Flowm/move-on-helium-sensors/doc/img/Gas.png

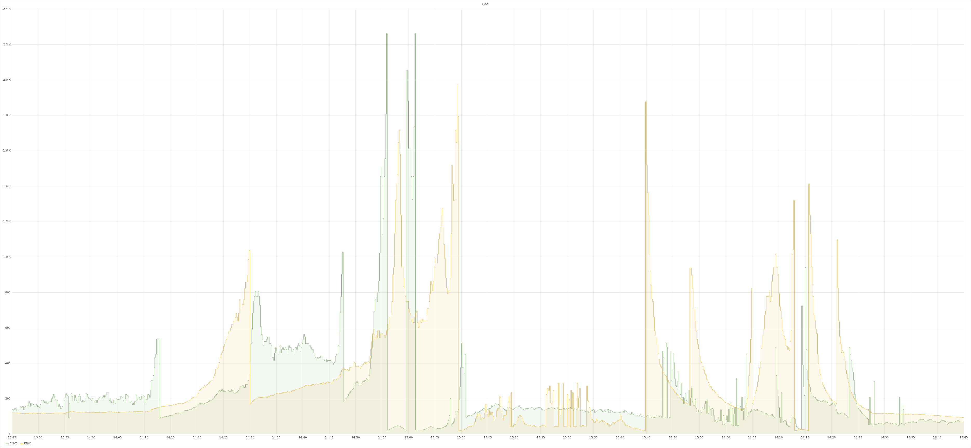
doc/img/Gas.png
