Flowm/move-on-helium-sensors/doc/img/TOSS_Photo.png

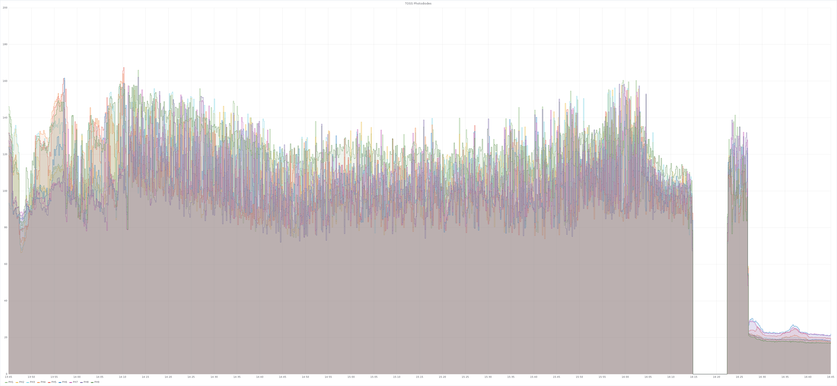
doc/img/TOSS_Photo.png
