Flowm/move-on-helium-sensors/src/modules/ADC/MPC320X.hpp

/*
 * MPC320X.h
 *
 *  Created on: Dec 16, 2017
 *      Author: tkale
 */
#pragma once

#include <mbed.h>

#define MPC_CHANNELS 8 // 0-7 : 8 channels on the MPC3208


/**
 * Driver for the MPC230X ADC's.
 * Configure the last digit of the device as the number of channels above.
 * WARNING: Only tested on the MPC2308!
 */
class MPC320X {
public:
    MPC320X(SPI &spi, DigitalOut &chipSelect) :
        spi(spi),
        chipSelect(chipSelect)
        {};
    /**
     * Read a adcs value from a single channel.
     * @param channel [0-7] : What channel to read.
     * @return
     */
    uint16_t getValueSingle(uint8_t channel);
    /**
     * Read a difference between 2 consecutive channels
     * TODO
     * @param channel
     * @return
     */
    uint16_t getValueDifferential(uint8_t channel);
    /**
     * Tests all channels in single ended mode and prints the result on stdout.
     */
    void testAllChannels();
private:
    //Interfaces
    SPI& spi;
    DigitalOut& chipSelect;
};
