Flowm/move-on-helium-sensors/tools/grafana/bin/sensor-parser/moveon-sen-parser.cpp

#include <cstdio>
#include <cstdint>
#include <cstddef>
#include <string>
#include "../../../../src/include/protocol_sensors.h"
#include <math.h>


float calculateDensity(float pressure, float temperature){

  //pressure [Pa], temperature [°C]
  //calculate current density [kg/m^3]

  int selector = 0;
  const float Rs = 287.1; //gas constant of air J/(kg*K);

  int N = 10;
  float nominaldensity[N] = {1.225, 3.899e-2, 1.774e-2, 3.972e-3, 1.057e-3, 3.206e-4, 8.77e-5, 1.905e-5, 3.396e-6, 5.297e-7};
  float basealtitude[N] = {0, 25, 30, 40, 50, 60, 70, 80, 90, 100};
  float scaleheight[N] = {7.249, 6.349, 6.682, 7.554, 8.382, 7.714, 6.549, 5.799, 5.382, 5.877};

  float density = pressure / (Rs * (temperature+273.15));
  for(int i = 0; i < N && density < nominaldensity[i]; i++) {
    selector = i;
  }

  float currentaltitudedensity = (basealtitude[selector] - log(density/nominaldensity[selector])*scaleheight[selector])*1000;
  return currentaltitudedensity;
}

float calculatePressure(float pressure){
  float currentaltitudepressure = - 8435 * log(pressure / 101325);
  return currentaltitudepressure;
}

int main(int argc, char **argv) {
    int c;
    int s = 0;
    int invalid = 0;
    char buf[1000];

    // Read binary data from stdin
    while((c = getchar()) != EOF) {
        buf[s++] = c;
    }

    printf("DBG SIZE=%d EXP=%d", s, sizeof(SensorDataNoGps));
    if (argc == 2) {
        invalid = std::stoi(argv[1]);
        printf(",CHK=%d", invalid);
    }
    printf("\r\n");

    // Invalid byte to packet size
    int invalid_range_start[8] = {};
    int invalid_count = 0;
    for (int i=0; i<8; i++) {
        if (invalid & (1 << i)) {
            invalid_count++;
            invalid_range_start[i] = 30 + 32 * i;
            printf("DBG Invalid Chunk %d from byte %d\n", i, invalid_range_start[i]);
        }
    }

    //if (invalid_count > 3) {
    //    printf("DBG Too many invalid chunks %d\n", invalid_count);
    //    return 1;
    //}

    // Cast to datastructure and print
    SensorDataNoGps* data = (SensorDataNoGps*) buf;

    //if (!(invalid & 0x01)) {
    for (int i = 0; i < MAX_ENV_SENSORS; i++) {
        printf("ENV%d "
               "TEMP=%.2f,HUM=%.2f,PRES=%.2f,GAS=%.4f,"
               "PALT=%.2f,DALT=%.2f"
               "\r\n",
               i,
               data->env[i].temperature,
               data->env[i].humidity,
               data->env[i].pressure,
               data->env[i].gasresistance,
               calculatePressure(data->env[i].pressure * 100),
               calculateDensity(data->env[i].pressure * 100, data->env[i].temperature));
    }
    //}

    //if (!(invalid & 0x03)) {
    printf("IMU "
           "ACC_X=%.4f,ACC_Y=%.4f,ACC_Z=%.4f,"
           "GYRO_X=%.4f,GYRO_Y=%.4f,GYRO_Z=%.4f,"
           "MAG_X=%.2f,MAG_Y=%.2f,MAG_Z=%.2f,"
           "ANG_X=%.4f,ANG_Y=%.4f,ANG_Z=%.4f,"
           //"QUAT_W=%.4f,QUAT_X=%.4f,QUAT_Y=%.4f,QUAT_Z=%.4f,"
           "TEMP_ACC=%d,"
           "RSTS=%u"
           "\r\n",
           data->imu.accel.x, data->imu.accel.y, data->imu.accel.z,
           data->imu.gyro.x, data->imu.gyro.y, data->imu.gyro.z,
           data->imu.mag.x, data->imu.mag.y, data->imu.mag.z,
           data->imu.orientation.x, data->imu.orientation.y, data->imu.orientation.z,
           //data->imu.quaternion.w, data->imu.quaternion.x, data->imu.quaternion.y, data->imu.quaternion.z,
           data->imu.temp_accel, //data->imu.temp_gyro,
           data->imu.resets);
    //}

    //if (!(invalid & 0x0C)) {
    printf("ADCS "
           //"ACC_X=%.4f,ACC_Y=%.4f,ACC_Z=%.4f,"
           "GYRO_X=%.4f,GYRO_Y=%.4f,GYRO_Z=%.4f,"
           "MAG_X=%.4f,MAG_Y=%.4f,MAG_Z=%.4f,"
           "SUN_X=%.4f,SUN_Y=%.4f,SUN_Z=%.4f,"
           "TEMP_OW1=%.4f,TEMP_OW2=%.4f,TEMP_OW3=%.4f,"
           "SUN_RAW1=%hu,SUN_RAW2=%hu,SUN_RAW3=%hu,SUN_RAW4=%hu"
           "\r\n",
           //data->adcs.accel.x, data->adcs.accel.y, data->adcs.accel.z,
           data->adcs.gyro.x, data->adcs.gyro.y, data->adcs.gyro.z,
           data->adcs.mag.x, data->adcs.mag.y, data->adcs.mag.z,
           data->adcs.sun.x, data->adcs.sun.y, data->adcs.sun.z,
           data->adcs.temp[0], data->adcs.temp[1], data->adcs.temp[2],
           data->adcs.raw_sun[0], data->adcs.raw_sun[1], data->adcs.raw_sun[2], data->adcs.raw_sun[3]);
    //}

    //if (!(invalid & 0x06)) {
    printf("OWT OW%d=%hd", 0, data->temp.temp[0]);
    for(int i = 1; i < MAX_TEMP_SENSORS; i++) {
        printf(",OW%d=%hd", i, data->temp.temp[i]);
    }
    printf("\r\n");
    //}

    //if (!(invalid & 0x18)) {
    printf("TOSS "
           "RTC=%u",
           data->toss.timestamp);
    for (int i = 0; i < 4; i++) {
        printf(",TMP%d=%hd", i+1, data->toss.temp[i]);
    }
    for (int i = 0; i < 9; i++) {
        printf(",PH%d=%hu", i+1, data->toss.photodiode[i]);
    }
    printf("\r\n");
    //}

    //if (!(invalid & 0x30)) {
    printf("SYS "
           "LOG_CNT=%hu,"
           "RTC_S=%hu,"
           "RTC_MS=%hu,"
           "LOG_MS=%hu,"
           "LOCK_US=%u,"
           "STATUS=%hu"
           "\r\n",
           data->system.log_cnt,
           data->system.rtc_s,
           data->system.rtc_ms,
           data->system.log_ms,
           data->system.lock_wait_us,
           data->system.sensor_status);
    //}

    return 0;
}
